strgaltdel/3in1/stl/Schwerpunkt/Gehaeusedeckel Unterseite.STL

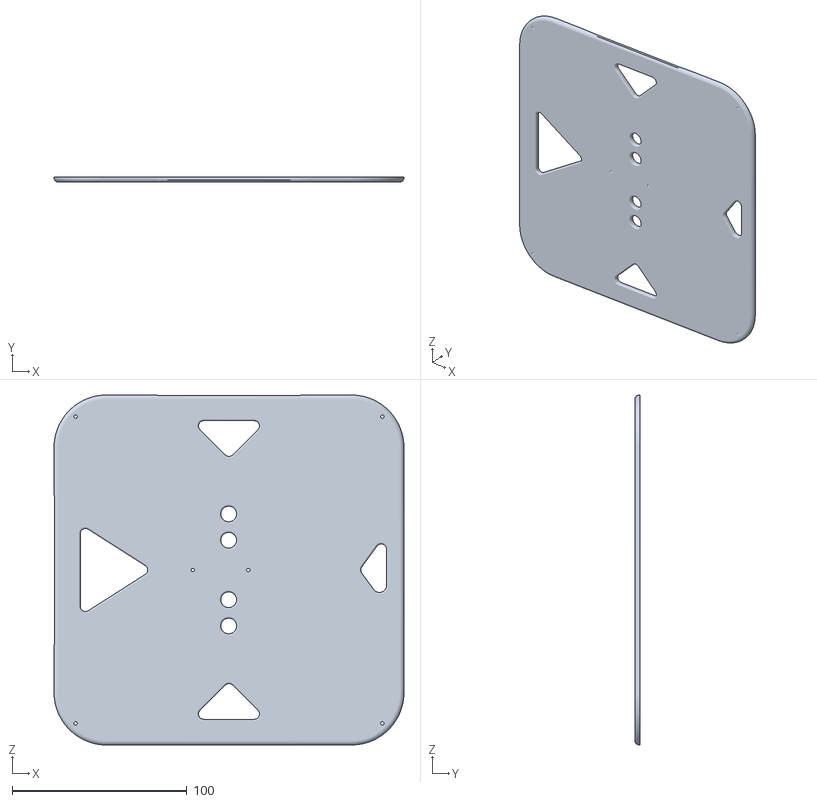
[picture p48: CAD file, 2020-12-01]
stl/Schwerpunkt/Gehaeusedeckel Unterseite.STL
200.0 x 3.00 x 200.0
