strgaltdel/3in1/stl/Headunit/Deckelplatte.STL

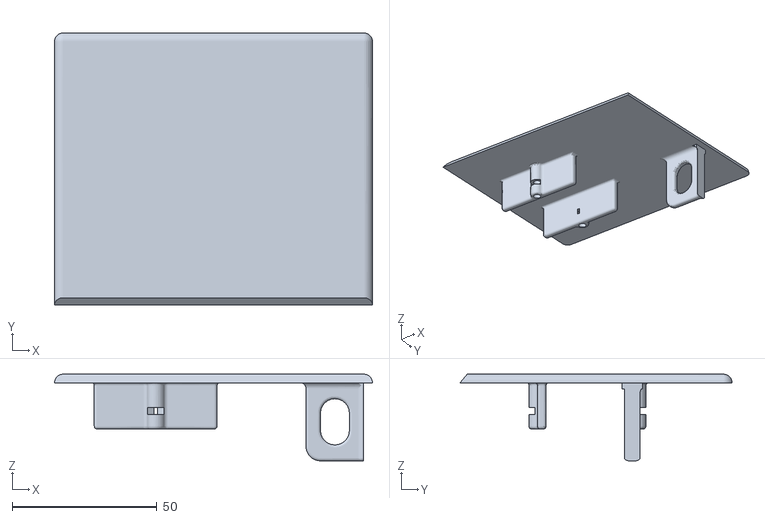
[picture p49: CAD file, 2020-12-01]
stl/Headunit/Deckelplatte.STL
110.0 x 94.1 x 30.0
