strgaltdel/3in1/stl/Schwerpunkt/Gehaeusedeckel links.STL

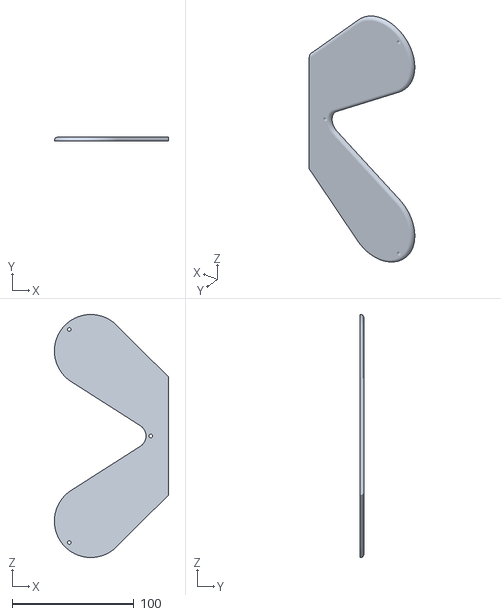
[picture p50: CAD file, 2020-12-01]
stl/Schwerpunkt/Gehaeusedeckel links.STL
94.0 x 3.00 x 200.0
