strgaltdel/3in1/stl/Schwerpunkt/Hinterer Modell-Traeger.STL

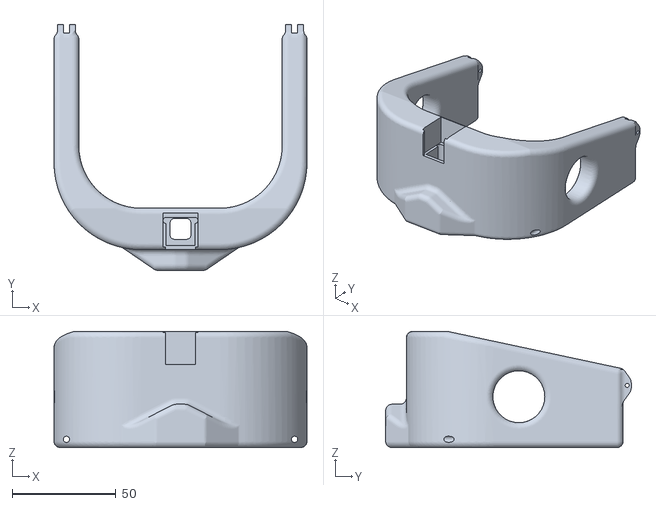
[picture p51: CAD file, 2020-12-01]
stl/Schwerpunkt/Hinterer Modell-Traeger.STL
122.0 x 118.5 x 56.0
