strgaltdel/3in1/3in1/includes_main.h

/* ***************************************************************************************
this code is part of "3in1.ino", an app to measure cg, incidence & deflection of rc models

##########################################################################################
##																						##
##  header file: 	includes_main.h														##
##  content:		all header files needed for app										##
##  date:			12 Oct 2020															##
##  rev.:			1.0																	##
##  by strgaltdel 																		##
##########################################################################################


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
**************************************************************************************/



#ifndef MASTERINCLUDES_H
#define MASTERINCLUDES_H

enum Status { WORKING, WAITING };
Status status;




#include <EEPROM.h>				// eeprom classes								standard lib	  https://www.arduino.cc/en/Reference/EEPROM

#include <Wire.h>				// imu communication  							https://github.com/jrowberg/i2cdevlib								// https://www.i2cdevlib.com
#include <TouchScreen.h>		// touch support								https://github.com/adafruit/Adafruit_TouchScreen
#include <Adafruit_GFX.h>		// used for rounded buttons						https://github.com/adafruit/Adafruit-GFX-Library
#include <MCUFRIEND_kbv.h>		// flexible lcd support							https://www.arduinolibraries.info/libraries/mcufriend_kbv
#include <Filters.h> 			// Filter classes for smoothing IMU data		https://github.com/JonHub/Filters/blob/master/Filters.h				// get filter classes
#include <HX711.h>				// load cell support	 						https://github.com/bogde/HX711					
#include <MovingAverage.h>		// simple way to build moving avg/used in cg	https://github.com/sofian/MovingAverage
#include <I2Cdev.h>				// some i2c, mpu6050 required methods			https://github.com/jrowberg/i2cdevlib


#include "custom.h"				// definitions / some colour customizing		## app coding

MCUFRIEND_kbv tft;

HX711 frontCell;  				// HX711 constructor (ada)
HX711 rearCell; 
//HX711_ADC frontCell(51, 49); 	//HX711_ADC lib: pins front sensor (DOUT, PD_SCK)
//HX711_ADC rearCell(47, 45); 



#include "lcd_config.h"			// lcd config, colours and touch calibration data		## app coding
#include "eeprom.h"				// eeprom class (storing and reading specific values)   ## app coding

#include "language.h"			// language file										## app coding
#include "touch.h"				// some tft relevant functions							## app coding
#include "imu.h"				// IMU class											## app coding	
#include "bitmaps_3in1.h"	
#include "buttons.h"			// buttons class										## app coding

//#include "screenServer.h"		// upload screens into processing client

#include "numpad.h"				// menue numpad											## app coding
#include "cg_main.h"			// menue cg scale										## app coding
#include "incidence_main.h"		// menue incidence meter								## app coding
#include "deflection_main.h"	// menue deflection										## app coding


#endif
