strgaltdel/3in1/3in1/bitmaps_3in1.h

/*
###################################################################################
#######																		#######
#######		      	  bitmaps for "3in1", a tool to measure					#######
#######	  			flap deflection, EWD & CG of flying rc gear				#######
#######																		#######
#######																		#######
#######																		#######
#######	 Rev 1.0															#######
#######	 20.02.20															#######
#######	 by strgaltdel														#######
###################################################################################

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
*************************************************************************************/

// 40x40 mono
const unsigned char CG[] PROGMEM = {
	
0x00, 0x00, 0xff, 0x00, 0x00, 
0x00, 0x0f, 0xff, 0xf0, 0x00, 
0x00, 0x1f, 0xf0, 0xf8, 0x00, 
0x00, 0x7f, 0xf0, 0x1e, 0x00, 
0x00, 0xff, 0xf0, 0x07, 0x00, 
0x03, 0xff, 0xf0, 0x01, 0xc0, 
0x07, 0xff, 0xf0, 0x00, 0xe0, 
0x07, 0xff, 0xf0, 0x00, 0x60, 
0x0f, 0xff, 0xf0, 0x00, 0x30, 
0x1f, 0xff, 0xf0, 0x00, 0x18, 
0x1f, 0xff, 0xf0, 0x00, 0x18, 
0x3f, 0xff, 0xf0, 0x00, 0x0c, 
0x7f, 0xff, 0xf0, 0x00, 0x0e, 
0x7f, 0xff, 0xf0, 0x00, 0x06, 
0x7f, 0xff, 0xf0, 0x00, 0x06, 
0x7f, 0xff, 0xf0, 0x00, 0x06, 
0xff, 0xff, 0xf0, 0x00, 0x03, 
0xff, 0xff, 0xf0, 0x00, 0x03, 
0xff, 0xff, 0xf0, 0x00, 0x03, 
0xff, 0xff, 0xf0, 0x00, 0x03, 
0xff, 0xff, 0xff, 0xff, 0xff, 
0xc0, 0x00, 0x1f, 0xff, 0xff, 
0xc0, 0x00, 0x1f, 0xff, 0xff, 
0xc0, 0x00, 0x1f, 0xff, 0xff, 
0x60, 0x00, 0x1f, 0xff, 0xfe, 
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
};
