strgaltdel/3in1/3in1/language.h

/* ***************************************************************************************
this code is part of "3in1.ino", an app to measure cg, incidence & deflection of rc models

##########################################################################################
##																						##
##  header file: 	language.h															##
##  content:		language specific strings											##
##  date:			12 Jan 2020															##
##  rev.:			1.0																	##
##  by strgaltdel 																		##
##########################################################################################


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
***************************************************************************************/




#define str_OK 				"  OK"
#define str_OK2 			"OK"
#define str_CANCEL			"Cancel"


// buttonsize XXL
#define str_CGSCALE			" SP Waage"
#define str_EWDSCALE		"   EWD   "
#define str_DEFLSCALE		"  Ruder  "
#define str_TARAXXL			"  Zero"

// buttonsize XL
#define str_TARA			"Zero"
#define str_BACK			"EXIT"
#define str_NEXT			"NEXT"
#define str_SAVE			"Save"
#define str_OK3				" OK "

// buttonsize MID 
#define str_CONFIG			"  Config"
#define str_TOG_Vtail		"Std <> V"
#define str_TOG_degsek		"thrw<>sec"

// buttonsize Small
#define str_CALIBRATE		"Calibrate"
#define str_edit			"  edit"
#define str_TOG_unit		" m <> i"

// cg_raw text
#define str_CGhead			"   Schwerpunktwaage"

// cg_cal text
#define str_CGcal0			"    Kalibrieren ?"
#define str_CGcal1			"Auflage vorne frei?"
#define str_CGcal1b			"Auflage vorne Last!"
#define str_CGcal1c			"   lese Auflage"
#define str_CGcal2			"Auflage hinten frei?"
#define str_CGcal2b			"Auflage hinten Last!"
#define str_CGcal2c			"   lese Auflage"
#define str_CGcal3			"void"
#define str_CGsave			"  speichere Daten"
#define str_CGtara			"   berechne Tara"

// cg_raw text
#define str_CGraw0			"Einzelmessung Zellen"
#define str_CGraw1			"  Vorne"
#define str_CGraw2			"  Hinten"


#define str_SET_flap		" set Flap"

#define str_CG_confTXT		"Konfiguration Waage"
#define str_CG_raw			" RohData"
#define str_CG_span			"Auflage"
#define str_CG_peg			"Anschlag"
#define str_CG_weight		"Gewicht"
#define str_CG_weight2		"Kalibrierungsmasse in "
#define str_CG_txt1			"Distanz in "
#define str_unit			"Mass"
#define str_unitA			"metrisch"
#define str_unitB			"imperial"


#define str_imuEWD0			" Flaeche"
#define str_imuEWD1			"  Hoehe"
#define str_imuEWD2			"  V Ltw"
#define str_imuFlap0		" Flap 0"
#define str_imuFlap1		" Flap 1"

#define str_wing			"Flaeche"
#define str_stab			"  LTW"
#define str_stabStd			" std.Ltw"
#define str_stabV			" V - Ltw"

//intro
#define str_Intro_1			"  Salmei"
#define str_Intro_2			"  Dalmei"
#define str_Intro_3			"  Adomei"

#define str_mm				"mm"
#define str_mm2				" (mm)"
#define str_inch			"in."
#define str_inch2			" (in.)"
#define str_g				"g"
#define str_g2				" (g)"
#define str_ounce			"oun."
#define str_ounce2			"(oun.)"
